lbarbisch/Maccaroni-Gun/Output V1.1/Magazin2_Stössel.stl

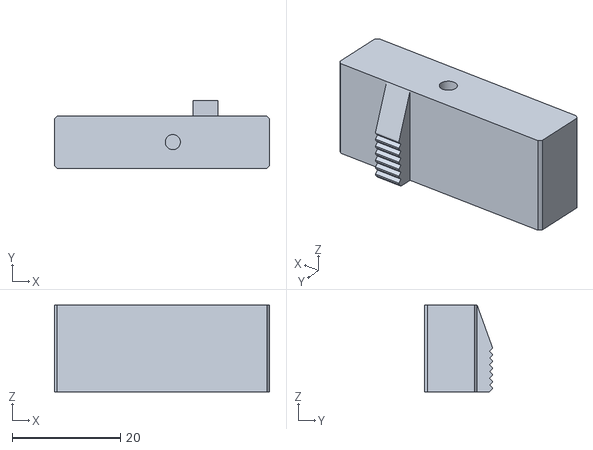
[picture p17: CAD file, 2024-10-05]
Output V1.1/Magazin2_Stössel.stl
39.7 x 12.5 x 16.0
