lbarbisch/Maccaroni-Gun/Output V1.1/Magazin.stl

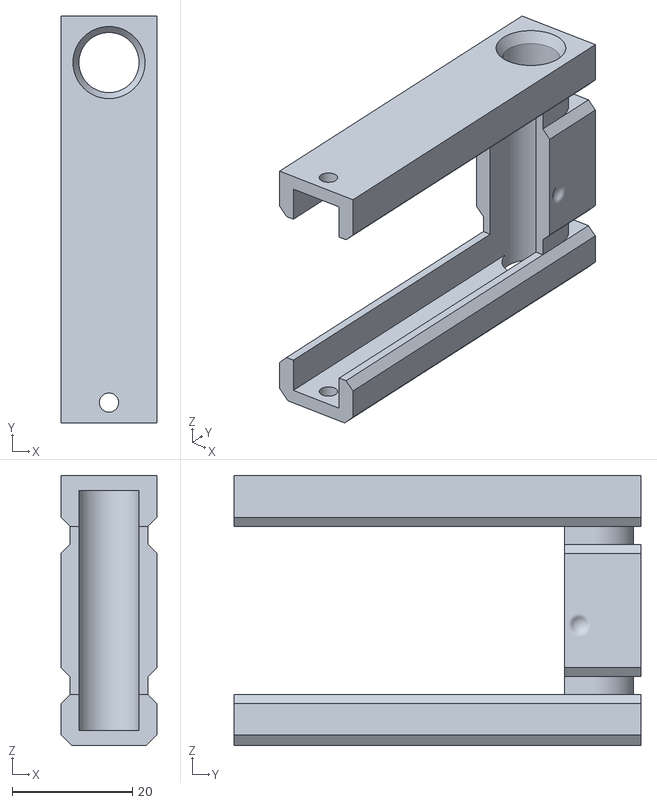
[picture p18: CAD file, 2024-10-05]
Output V1.1/Magazin.stl
16.0 x 67.8 x 45.0
