lbarbisch/Maccaroni-Gun/Output V1.1/Picatinny Rail short.stl

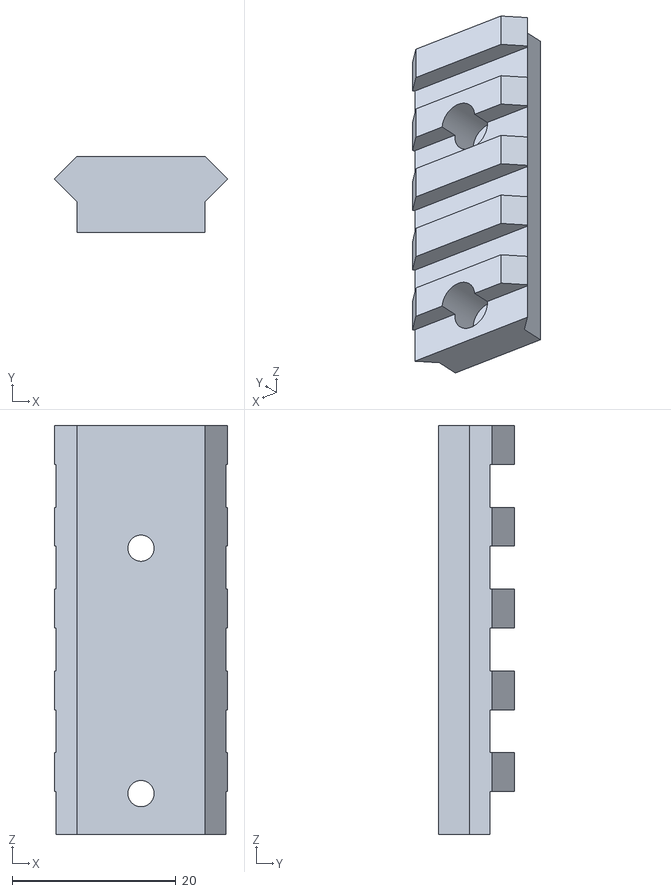
[picture p19: CAD file, 2024-10-05]
Output V1.1/Picatinny Rail short.stl
21.2 x 9.32 x 50.0
