lbarbisch/Maccaroni-Gun/Output V1.1/Hauptschalter.stl

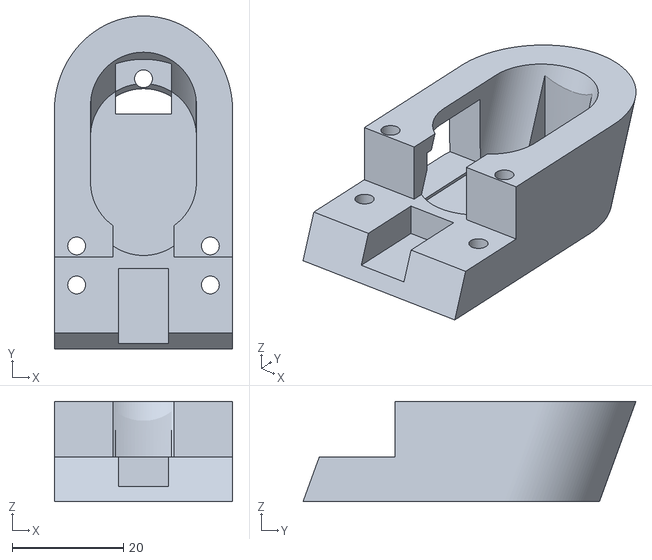
[picture p20: CAD file, 2024-07-16]
Output V1.1/Hauptschalter.stl
32.0 x 59.8 x 18.0
