lbarbisch/Maccaroni-Gun/Output V1.1/Stiftleiste_Halter.stl

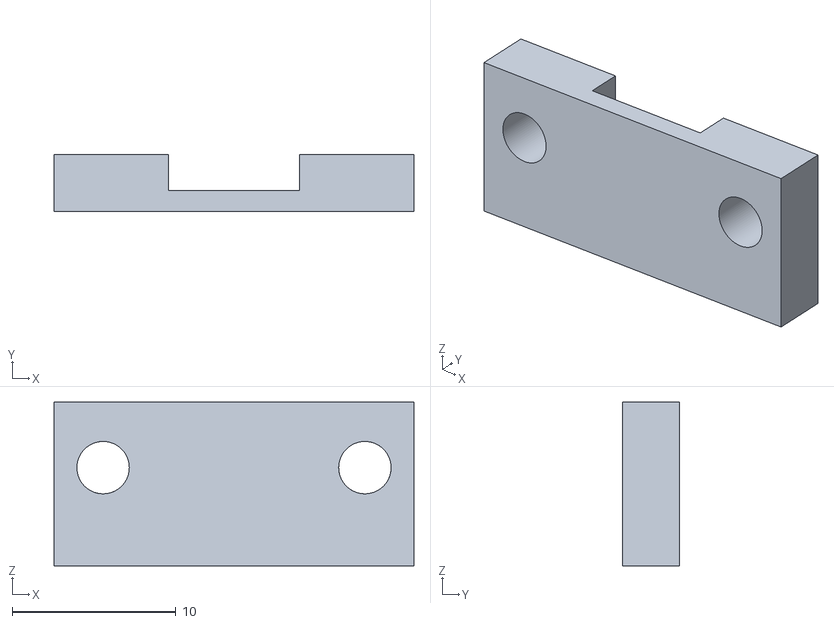
[picture p21: CAD file, 2024-07-16]
Output V1.1/Stiftleiste_Halter.stl
22.0 x 3.50 x 10.0
