lbarbisch/Maccaroni-Gun/Output V1.1/Abzughalter.stl

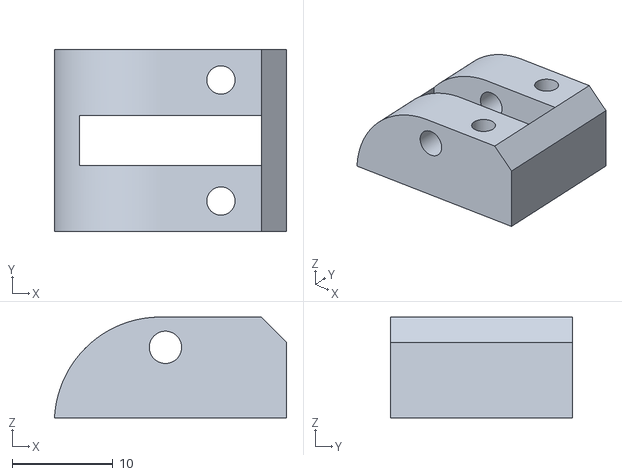
[picture p22: CAD file, 2024-07-16]
Output V1.1/Abzughalter.stl
23.0 x 18.0 x 10.0
