lbarbisch/Maccaroni-Gun/Software/Driveunit_Fan/Core/Inc/main.h

#define Trigger_Pin GPIO_PIN_15
#define Trigger_GPIO_Port GPIOC
#define ADC_Angle_Pin GPIO_PIN_0
#define ADC_Angle_GPIO_Port GPIOA
#define ADC_I_U_Pin GPIO_PIN_4
#define ADC_I_U_GPIO_Port GPIOA
#define ADC_I_V_Pin GPIO_PIN_5
#define ADC_I_V_GPIO_Port GPIOA
#define ADC_VIN_Pin GPIO_PIN_7
#define ADC_VIN_GPIO_Port GPIOA
#define PWM_U_Pin GPIO_PIN_8
#define PWM_U_GPIO_Port GPIOA
#define PWM_V_Pin GPIO_PIN_11
#define PWM_V_GPIO_Port GPIOA
#define PWM_Enable_Pin GPIO_PIN_12
#define PWM_Enable_GPIO_Port GPIOA
#define PWM_W_Pin GPIO_PIN_3
#define PWM_W_GPIO_Port GPIOB
