lbarbisch/Maccaroni-Gun/Software/Driveunit_Fan/Core/Inc/sintab.h

/*
 * sintab.h
 *
 *  Created on: Mar 25, 2024
 *      Author: Lukas
 */

#ifndef INC_SINTAB_H_
#define INC_SINTAB_H_

#include <stdint.h>

static const uint16_t sintablen = 2048;

static const int16_t sintab[2048] = {
		0, 22, 43, 65, 87, 109, 131, 153, 175, 196, 218, 239, 261, 282, 303, 324, 345,
		365, 386, 406, 426, 446, 466, 485, 504, 523, 542, 561, 579, 597, 615, 632, 649, 666,
		683, 699, 715, 730, 746, 761, 775, 789, 803, 817, 830, 842, 855, 867, 878, 889, 900,
		910, 920, 929, 938, 947, 955, 963, 970, 977, 983, 989, 994, 999, 1004, 1008, 1012, 1015,
		1017, 1020, 1021, 1022, 1023, 1023, 1023, 1023, 1022, 1020, 1018, 1015, 1012, 1009, 1005, 1000, 996,
		990, 984, 978, 972, 964, 957, 949, 940, 931, 922, 912, 902, 892, 880, 869, 857, 845,
		832, 819, 806, 792, 778, 764, 749, 734, 718, 702, 686, 670, 653, 636, 619, 601, 583,
		565, 546, 528, 509, 489, 470, 450, 430, 410, 390, 370, 349, 328, 307, 286, 265, 244,
		222, 201, 179, 158, 136, 114, 92, 70, 48, 26, 4, -17, -39, -61, -83, -105, -126,
		-148, -170, -192, -213, -235, -256, -277, -298, -319, -340, -361, -381, -402, -422, -442, -462, -481,
		-500, -519, -538, -557, -575, -593, -611, -629, -646, -663, -679, -696, -712, -727, -742, -757, -772,
		-786, -800, -814, -827, -840, -852, -864, -876, -887, -898, -908, -918, -927, -937, -945, -953, -961,
		-969, -975, -982, -988, -993, -998, -1003, -1007, -1011, -1014, -1017, -1019, -1021, -1022, -1023, -1023, -1023,
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
		990, 995, 1000, 1005, 1009, 1012, 1015, 1018, 1020, 1021, 1023, 1023, 1023, 1023, 1023, 1021, 1020,
		1018, 1015, 1012, 1008, 1004, 1000, 995, 989, 984, 977, 971, 963, 956, 948, 939, 930, 921,
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
};

#endif /* INC_SINTAB_H_ */
